kivancsikert/chicken-coop-door/include/Config.h

#pragma once

#include <ArduinoJson.h>

#include "FileSystemHandler.h"

class Config {
public:
    Config(FileSystemHandler& fileSystem)
        : fileSystem(fileSystem) {
    }

    void begin(bool reset);
    void update(const JsonDocument& json);
    void store();

    /**
     * Light required to be above limit to open the door.
     */
    float openLightLimit;

    /**
     * Light required to be below limit to open the door.
     */
    float closeLightLimit;

    /**
     * Light sensor update interval in milliseconds.
     */
    unsigned long lightUpdateInterval;

    /**
     * The size of the moving window to abserve to smooth over light fluctuations.
     */
    unsigned long lightLatencyInterval;

    /**
     * Is moving the door enabled?
     */
    bool motorEnabled;

    /**
     * Maximum time in milliseconds to take to open or close the door.
     * After that time the motor will stop and the door will be disabled.
     */
    unsigned long movementTimeout;

    /**
     * Whether to invert the "gate open" switch or not.
     */
    bool invertOpenSwitch;

    /**
     * Whether to invert the "gate close" switch or not.
     */
    bool invertCloseSwitch;

    /**
     * WIFI SSID to connect to.
     */
    String wifiSsid;

    /**
     * WIFI SSID to connect to.
     */
    String wifiPassword;

    /**
     * WIFI connection timeout.
     */
    unsigned long wifiConnectionTimeout;

    /**
     * Number of milliseconds between publishing state.
     */
    unsigned long statePublishingInterval;

private:
    void serialize(JsonDocument& json);

    FileSystemHandler& fileSystem;
};

class ConfigAware {
public:
    ConfigAware(const Config& config)
        : config(config) {
    }

protected:
    const Config& config;
};
